ArcadiaE/Badminton-Motion-Detection-Device/Data_Process/Matlab/pre_test_20250307_1254.csv

timestamp | roll | pitch | yaw | heartRate | spo2 | roll_velocity | pitch_velocity | yaw_velocity | roll_acceleration | pitch_acceleration | yaw_acceleration | peak_count
0.0000 | 0.4935 | 0.5032 | 0.5115 | 0.0000 | 0.0000 | 0.0000 | 0.0000 | 0.0000 | 0.0000 | 0.0000 | 0.0000 | 0
0.1963 | 0.4944 | 0.5041 | 0.5151 | 0.0000 | 0.0000 | 0.0953 | 0.0864 | 0.3587 | 9.5296 | 8.6433 | 35.8689 | 0
0.3924 | 0.4958 | 0.5036 | 0.5178 | 0.0000 | 0.0000 | 0.1379 | -0.0539 | 0.2680 | 4.2650 | -14.0375 | -9.0677 | 0
0.6959 | 0.4967 | 0.5035 | 0.5197 | 0.0000 | 0.0000 | 0.0920 | -0.0098 | 0.1949 | -4.5943 | 4.4149 | -7.3099 | 1
0.9029 | 0.4967 | 0.5038 | 0.5218 | 0.0000 | 0.0000 | -0.0022 | 0.0330 | 0.2083 | -9.4250 | 4.2814 | 1.3417 | 1
1.5156 | 0.4964 | 0.5050 | 0.5281 | 0.0000 | 0.0000 | -0.0325 | 0.1155 | 0.6308 | -3.0246 | 8.2463 | 42.2514 | 1
2.1148 | 0.4962 | 0.5056 | 0.5287 | 0.0000 | 0.0000 | -0.0244 | 0.0644 | 0.0621 | 0.8073 | -5.1069 | -56.8700 | 1
2.7769 | 0.4961 | 0.5058 | 0.5287 | 0.0000 | 0.0000 | -0.0080 | 0.0239 | 0.0000 | 1.6454 | -4.0531 | -6.2144 | 1
3.3765 | 0.4961 | 0.5058 | 0.5287 | 0.0000 | 0.0000 | 0.0000 | 0.0000 | 0.0000 | 0.7966 | -2.3884 | 0.0000 | 1
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
