ArcadiaE/Badminton-Motion-Detection-Device/Data_Process/Matlab/pre_test_20250307_1303.csv

timestamp | roll | pitch | yaw | heartRate | spo2 | roll_velocity | pitch_velocity | yaw_velocity | roll_acceleration | pitch_acceleration | yaw_acceleration | peak_count
0.0001 | 0.0000 | 0.5000 | 0.4991 | 0.0000 | 0.0000 | 0.0000 | 0.0000 | 0.0000 | 0.0000 | 0.0000 | 0.0000 | 0
0.1960 | 0.5000 | 0.5000 | 0.4991 | 0.0000 | 0.0000 | 49.9966 | 0.0000 | 0.0000 | 4999.6606 | 0.0000 | 0.0000 | 0
0.3600 | 0.5000 | 0.5000 | 0.4991 | 0.0000 | 0.0000 | 0.0000 | 0.0000 | 0.0000 | -4999.6606 | 0.0000 | 0.0000 | 1
0.5110 | 0.5000 | 0.5000 | 0.4991 | 0.0000 | 0.0000 | 0.0000 | 0.0000 | 0.0000 | 0.0000 | 0.0000 | 0.0000 | 1
0.7488 | 0.5000 | 0.5000 | 0.4991 | 0.0000 | 0.0000 | 0.0000 | 0.0000 | 0.0000 | 0.0000 | 0.0000 | 0.0000 | 1
0.9266 | 0.5000 | 0.5000 | 0.4991 | 0.0000 | 0.0000 | 0.0000 | 0.0000 | 0.0000 | 0.0000 | 0.0000 | 0.0000 | 1
1.3759 | 0.5000 | 0.5000 | 0.4991 | 0.0000 | 0.0000 | 0.0000 | 0.0000 | 0.0000 | 0.0000 | 0.0000 | 0.0000 | 1
1.9786 | 0.5000 | 0.5000 | 0.4991 | 0.0000 | 0.0000 | 0.0000 | 0.0000 | 0.0000 | 0.0000 | 0.0000 | 0.0000 | 1
2.5784 | 0.5000 | 0.5000 | 0.4991 | 0.0000 | 0.0000 | 0.0000 | 0.0000 | 0.0000 | 0.0000 | 0.0000 | 0.0000 | 1
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
