ArcadiaE/Badminton-Motion-Detection-Device/Data_Process/Matlab/pre_test_20250307_1304.csv

timestamp | roll | pitch | yaw | heartRate | spo2 | roll_velocity | pitch_velocity | yaw_velocity | roll_acceleration | pitch_acceleration | yaw_acceleration | peak_count
0.0000 | 0.0000 | 0.0000 | 0.0000 | 0.0000 | 0.0000 | 0.0000 | 0.0000 | 0.0000 | 0.0000 | 0.0000 | 0.0000 | 0
0.1997 | 0.0000 | 0.0000 | 0.0000 | 0.0000 | 0.0000 | 0.0000 | 0.0000 | 0.0000 | 0.0000 | 0.0000 | 0.0000 | 0
0.3760 | 0.0000 | 0.0000 | 0.0000 | 0.0000 | 0.0000 | 0.0000 | 0.0000 | 0.0000 | 0.0000 | 0.0000 | 0.0000 | 0
0.5711 | 0.0000 | 0.0000 | 0.0000 | 0.0000 | 0.0000 | 0.0000 | 0.0000 | 0.0000 | 0.0000 | 0.0000 | 0.0000 | 0
0.7803 | 0.0000 | 0.0000 | 0.0000 | 0.0000 | 0.0000 | 0.0000 | 0.0000 | 0.0000 | 0.0000 | 0.0000 | 0.0000 | 0
1.0835 | 0.0000 | 0.0000 | 0.0000 | 0.0000 | 0.0000 | 0.0000 | 0.0000 | 0.0000 | 0.0000 | 0.0000 | 0.0000 | 0
1.6793 | 0.5000 | 0.4998 | 0.5113 | 0.0000 | 0.0000 | 49.9974 | 49.9751 | 51.1307 | 4999.7388 | 4997.5103 | 5113.0659 | 0
2.2837 | 0.4999 | 0.4996 | 0.5184 | 0.0000 | 0.0000 | -0.0078 | -0.0187 | 0.7128 | -5000.5151 | -4999.3809 | -5041.7852 | 1
2.8793 | 0.5002 | 0.4995 | 0.5343 | 0.0000 | 0.0000 | 0.0265 | -0.0099 | 1.5872 | 3.4240 | 0.8786 | 87.4400 | 1
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
