ArcadiaE/Badminton-Motion-Detection-Device/Data_Process/Matlab/pre_test_20250313_1145.csv

timestamp | roll | pitch | yaw | heartRate | spo2 | roll_velocity | pitch_velocity | yaw_velocity | roll_acceleration | pitch_acceleration | yaw_acceleration | peak_count
0.0000 | 0.0000 | 0.0000 | 0.0000 | 0.0000 | 0.0000 | 0.0000 | 0.0000 | 0.0000 | 0.0000 | 0.0000 | 0.0000 | 0
0.4725 | 0.0000 | 0.0000 | 0.0000 | 0.0000 | 0.0000 | 0.0000 | 0.0000 | 0.0000 | 0.0000 | 0.0000 | 0.0000 | 0
1.1843 | 0.0000 | 0.0000 | 0.0000 | 0.0000 | 0.0000 | 0.0000 | 0.0000 | 0.0000 | 0.0000 | 0.0000 | 0.0000 | 0
1.8439 | 0.0000 | 0.0000 | 0.0000 | 0.0000 | 0.0000 | 0.0000 | 0.0000 | 0.0000 | 0.0000 | 0.0000 | 0.0000 | 0
2.5036 | 0.0000 | 0.0000 | 0.0000 | 0.0000 | 0.0000 | 0.0000 | 0.0000 | 0.0000 | 0.0000 | 0.0000 | 0.0000 | 0
3.1034 | 0.0000 | 0.0000 | 0.0000 | 0.0000 | 0.0000 | 0.0000 | 0.0000 | 0.0000 | 0.0000 | 0.0000 | 0.0000 | 0
3.7067 | 0.0000 | 0.0000 | 0.0000 | 0.0000 | 0.0000 | 0.0000 | 0.0000 | 0.0000 | 0.0000 | 0.0000 | 0.0000 | 0
4.3017 | 0.0000 | 0.4992 | 0.4369 | 0.0000 | 0.0000 | 0.0000 | 49.9210 | 43.6910 | 0.0000 | 4992.1011 | 4369.1040 | 0
4.9029 | 0.4909 | 0.4985 | 0.3370 | 0.0000 | 0.0000 | 49.0884 | -0.0718 | -9.9909 | 4908.8438 | -4999.2812 | -5368.1895 | 0
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
